JohnnyGOX17/4ch-RF-FE/docs/components/Power/WEBENCH_TPS562208.pdf

## WEBENCH ® Design Report

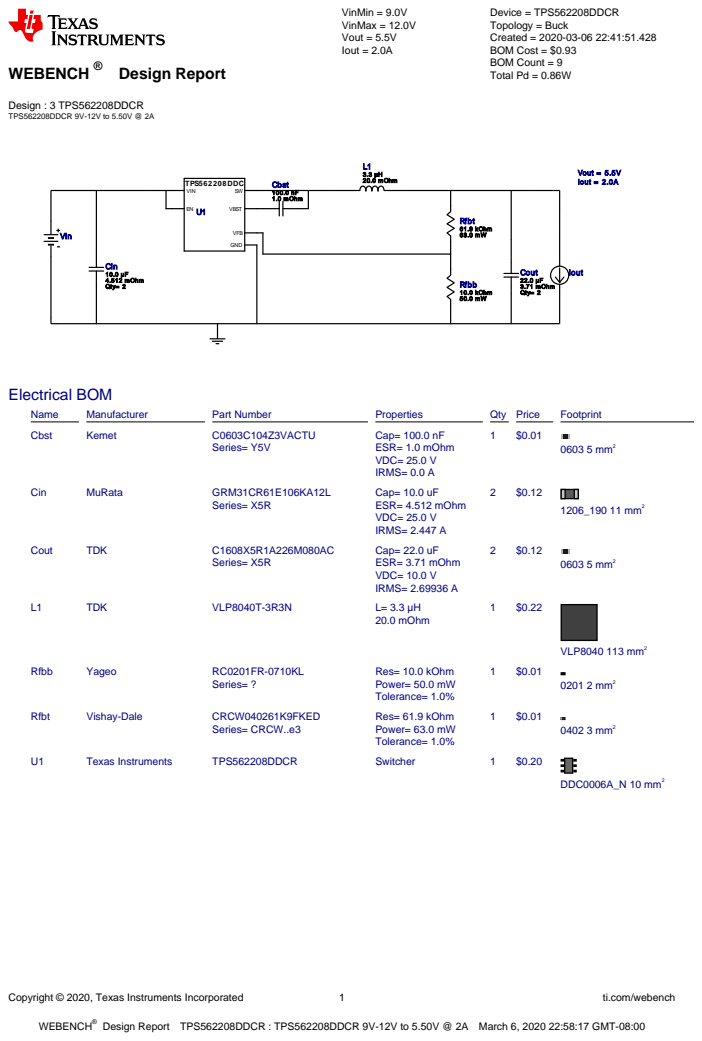
[picture p6: page 1]
Copyright © 2020, Texas Instruments Incorporated; ti.com/webench; WEBENCH®; Design : 3 TPS562208DDCR TPS562208DDCR 9V-12V to 5.50V @ 2A; VinMin = 9.0V VinMax = 12.0V Vout = 5.5V Iout = 2.0A; Device = TPS562208DDCR Topology = Buck Created = 2020-03-06 22:41:51.428 BOM Cost = $0.93 BOM Count = 9 Total Pd = 0.86W; Vout = 5.5V Iout = 2.0A; Rfbb 10.0 kOhm 50.0 mW; Cbst 100.0 nF 1.0 mOhm; Cout 22.0 µF 3.71 mOhm Qty= 2; TPS562208DDC; GND; VIN; VFB; VBST U1; L1 3.3 µH 20.0 mOhm; Rfbt 61.9 kOhm 63.0 mW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

Design Report TPS562208DDCR : TPS562208DDCR 9V-12V to 5.50V @ 2A March 6, 2020 22:58:17 GMT-08:00

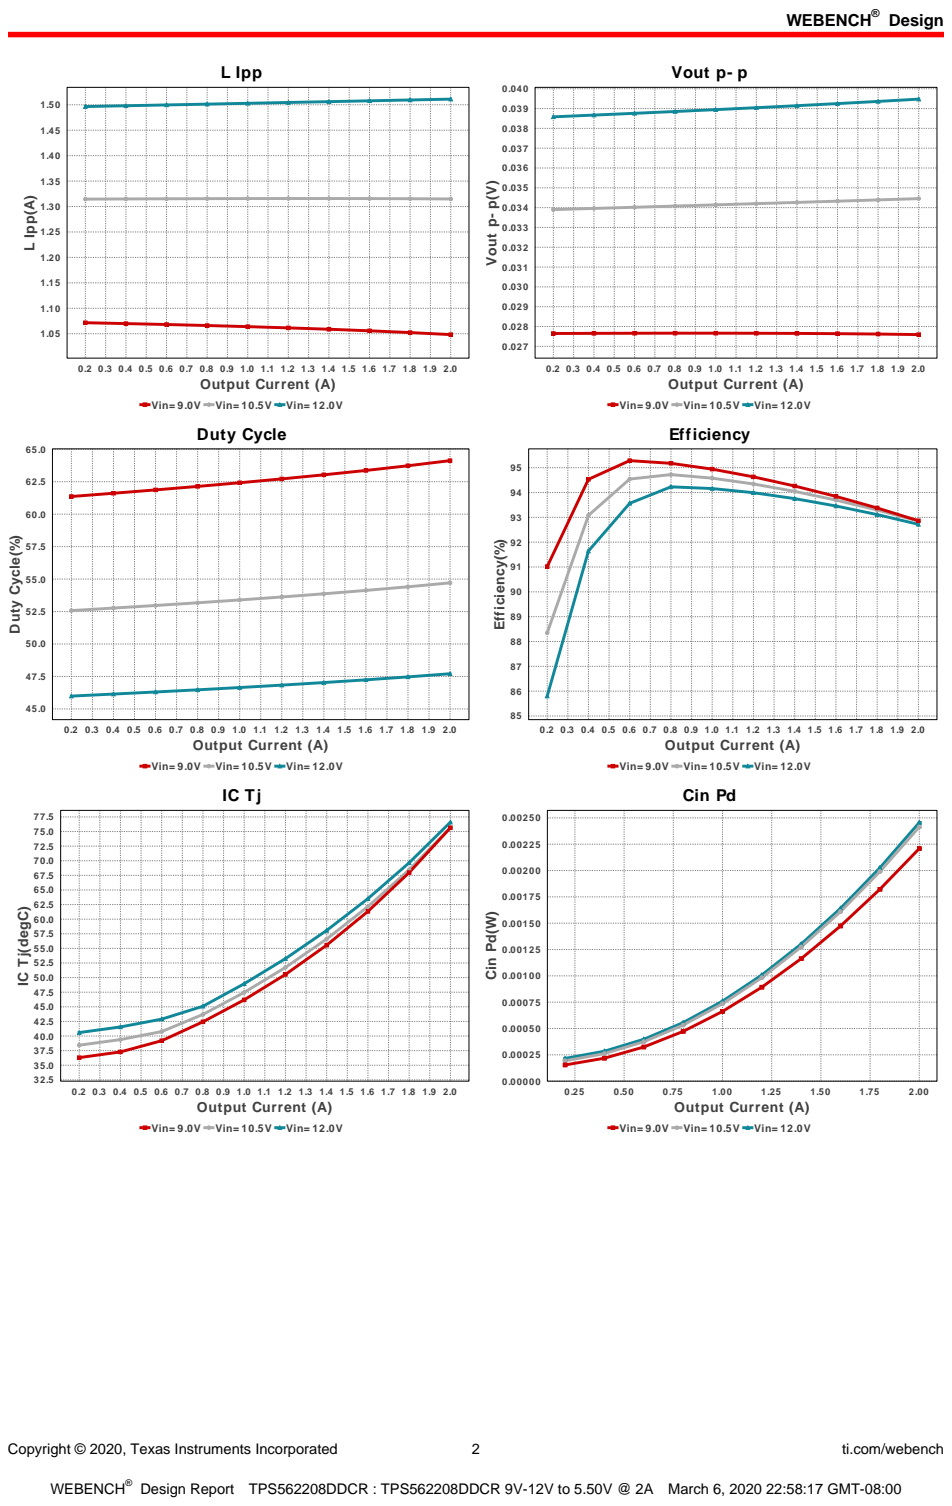
[picture p7: page 2]
Design; Copyright © 2020, Texas Instruments Incorporated; ti.com/webench; L Ipp; 0.2 0.3 0.4 0.5 0.6 0.7 0.8 0.9 1.0 1.1 1.2 1.3 1.4 1.5 1.6 1.7 1.8 1.9 2.0 Output Current (A); L Ipp(A); Vout p- p; Vout p- p(V); Duty Cycle(%); Efficiency(%); Cin Pd; 2.00 Output Current (A); Cin Pd(W)

Vin= 9.0V Vin= 10.5V Vin= 12.0V
Duty Cycle

Efficiency

IC Tj(degC)

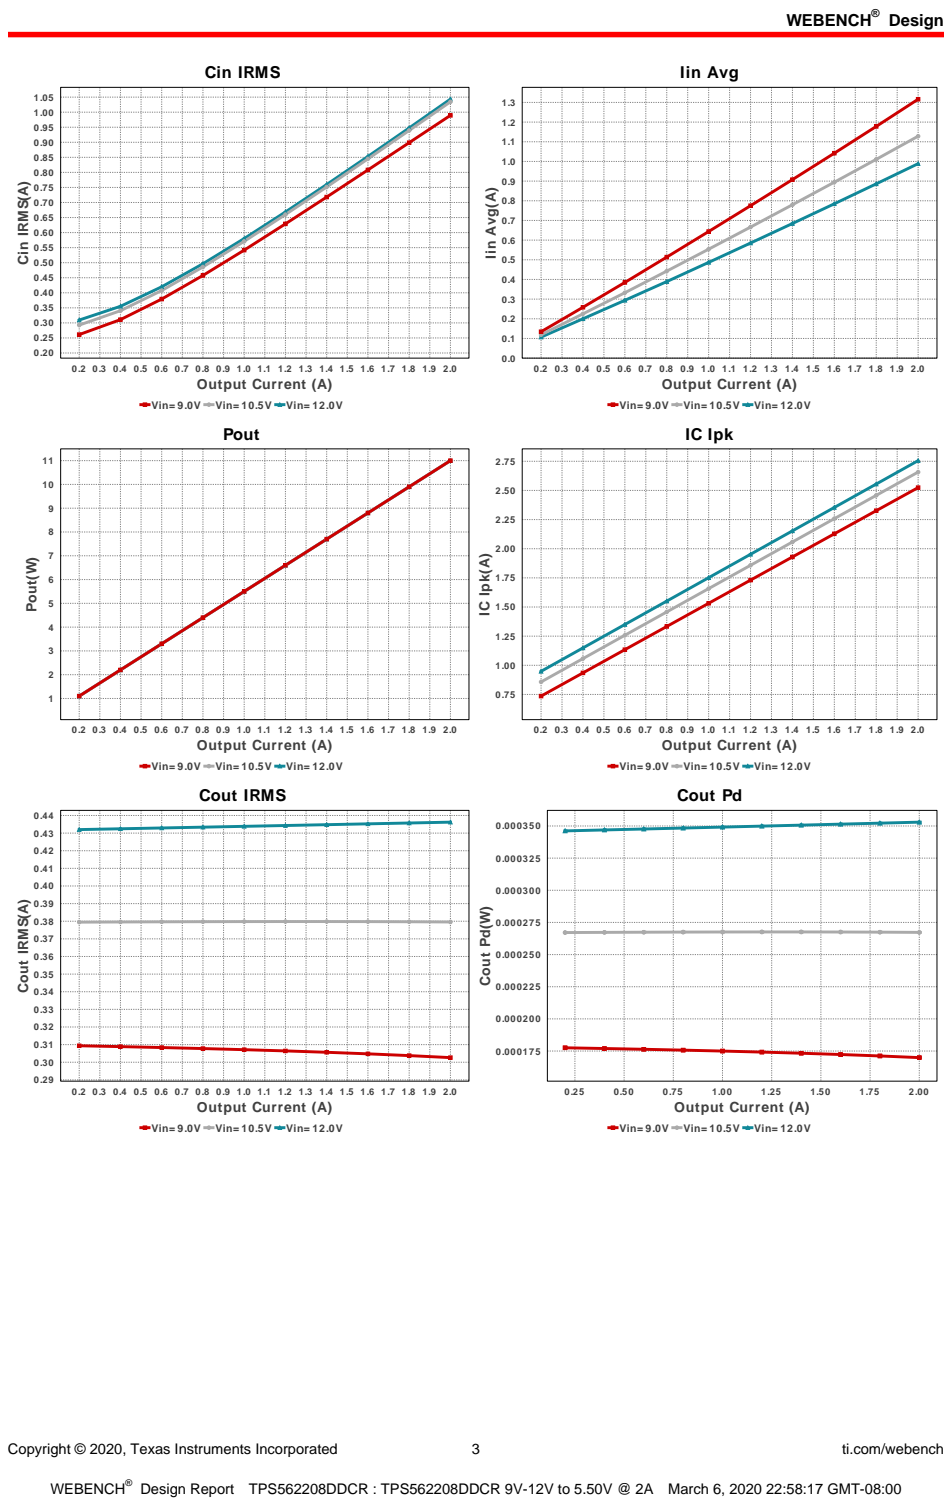
[picture p8: page 3]
Copyright © 2020, Texas Instruments Incorporated; ti.com/webench; Cin IRMS; 0.2 0.3 0.4 0.5 0.6 0.7 0.8 0.9 1.0 1.1 1.2 1.3 1.4 1.5 1.6 1.7 1.8 1.9 2.0 Output Current (A); Cin IRMS(A); Iin Avg; Iin Avg(A); Pout; Pout(W); IC Ipk; IC Ipk(A); Cout IRMS(A); 2.00 Output Current (A); Cout Pd(W)

Vin= 9.0V Vin= 10.5V Vin= 12.0V

Cout IRMS

Cout Pd

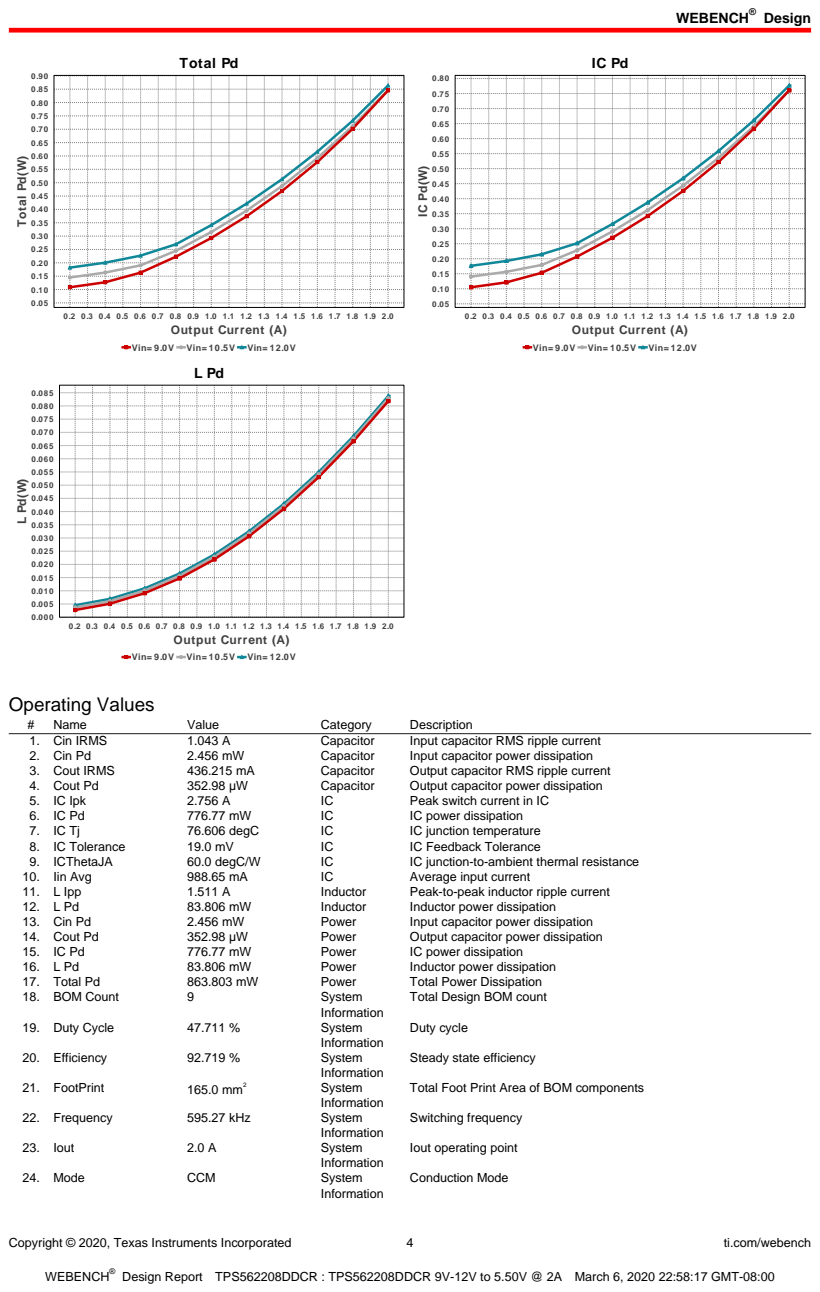
[picture p9: page 4]
Copyright © 2020, Texas Instruments Incorporated; ti.com/webench; Total Pd; 0.2 0.3 0.4 0.5 0.6 0.7 0.8 0.9 1.0 1.1 1.2 1.3 1.4 1.5 1.6 1.7 1.8 1.9 2.0 Output Current (A); Total Pd(W); Operating Values; Name; Value; Category; Description; 1. Cin IRMS; Capacitor; Input capacitor RMS ripple current; 2. Cin Pd; Input capacitor power dissipation; 3. Cout IRMS; Output capacitor RMS ripple current; 4. Cout Pd; Output capacitor power dissipation; 5. IC Ipk; Peak switch current in IC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

Vin= 9.0V Vin= 10.5V Vin= 12.0V

Total Design BOM count

Steady state efficiency

Total Foot Print Area of BOM components

Iout operating point

Copyright © 2020, Texas Instruments Incorporated | 5 | ti.com/webench
# | Name | Value | Category | Description

25. Pout | 11.0 W | System
| | | Information | Total output power
26. Total BOM | $0.93 | System
| | | Information | Total BOM Cost
27. Vin | 12.0 V | System
| | | Information | Vin operating point
28. Vout | 5.5 V | System
| | | Information | Operational Output Voltage
29. Vout Actual | 5.5 V | System
| | | Information | Vout Actual calculated based on selected voltage divider resistors
30. Vout Tolerance | 4.266 % | System
| | | Information | Vout Tolerance based on IC Tolerance (no load) and voltage divider resistors if applicable
31. Vout p-p | 39.476 mV | System
| | | Information | Peak-to-peak output ripple voltage

## Design Inputs

Name | Value | Description
Iout | 2.0 | Maximum Output Current
VinMax | 12.0 | Maximum input voltage
VinMin | 9.0 | Minimum input voltage
Vout | 5.5 | Output Voltage
| base_pn | | TPS562208 | Base Product Number
source | DC | Input Source Type
Ta | 30.0 | Ambient temperature


Copyright © 2020, Texas Instruments Incorporated | 6 | ti.com/webench

## Assembly

## Component Testing

Some published data on components in datasheets such as Capacitor ESR and Inductor DC resistance is based on conservative values that will guarantee that the components always exceed the specification. For design purposes it is usually better to work with typical values. Since this data is not always available it is a good practice to measure the Capacitance and ESR values of Cin and Cout, and the inductance and DC resistance of L1 before assembly of the board. Any large discrepancies in values should be electrically simulated in WEBENCH to check for instabilities and thermally simulated in WebTHERM to make sure critical temperatures are not exceeded.

## Soldering Component to Board

If board assembly is done in house it is best to tack down one terminal of a component on the board then solder the other terminal. For surface mount parts with large tabs, such as the DPAK, the tab on the back of the package should be pre-tinned with solder, then tacked into place by one of the pins. To solder the tab town to the board place the iron down on the board while resting against the tab, heating both surfaces simultaneously. Apply light pressure to the top of the plastic case until the solder flows around the part and the part is flush with the PCB. If the solder is not flowing around the board you may need a higher wattage iron (generally 25W to 30W is enough).

## Initial Startup of Circuit

It is best to initially power up the board by setting the input supply voltage to the lowest operating input voltage 9.0V and set the input supply's current limit to zero. With the input supply off connect up the input supply to Vin and GND. Connect a digital volt meter and a load if needed to set the minimum Iout of the design from Vout and GND. Turn on the input supply and slowly turn up the current limit on the input supply. If the voltage starts to rise on the input supply continue increasing the input supply current limit while watching the output voltage. If the current increases on the input supply, but the voltage remains near zero, then there may be a short or a component misplaced on the board. Power down the board and visually inspect for solder bridges and recheck the diode and capacitor polarities. Once the power supply circuit is operational then more extensive testing may include full load testing, transient load and line tests to compare with simulation results.

## Load Testing

The setup is the same as the initial startup, except that an additional digital voltmeter is connected between Vin and GND, a load is connected between Vout and GND and a current meter is connected in series between Vout and the load. The load must be able to handle at least rated output power + 50% ( 7.5 watts for this design). Ideally the load is supplied in the form of a variable load test unit. It can also be done in the form of suitably large power resistors. When using an oscilloscope to measure waveforms on the prototype board, the ground leads of the oscilloscope probes should be as short as possible and the area of the loop formed by the ground lead should be kept to a minimum. This will help reduce ground lead inductance and eliminate EMI noise that is not actually present in the circuit.

## WEBENCH® Electrical Simulation Report

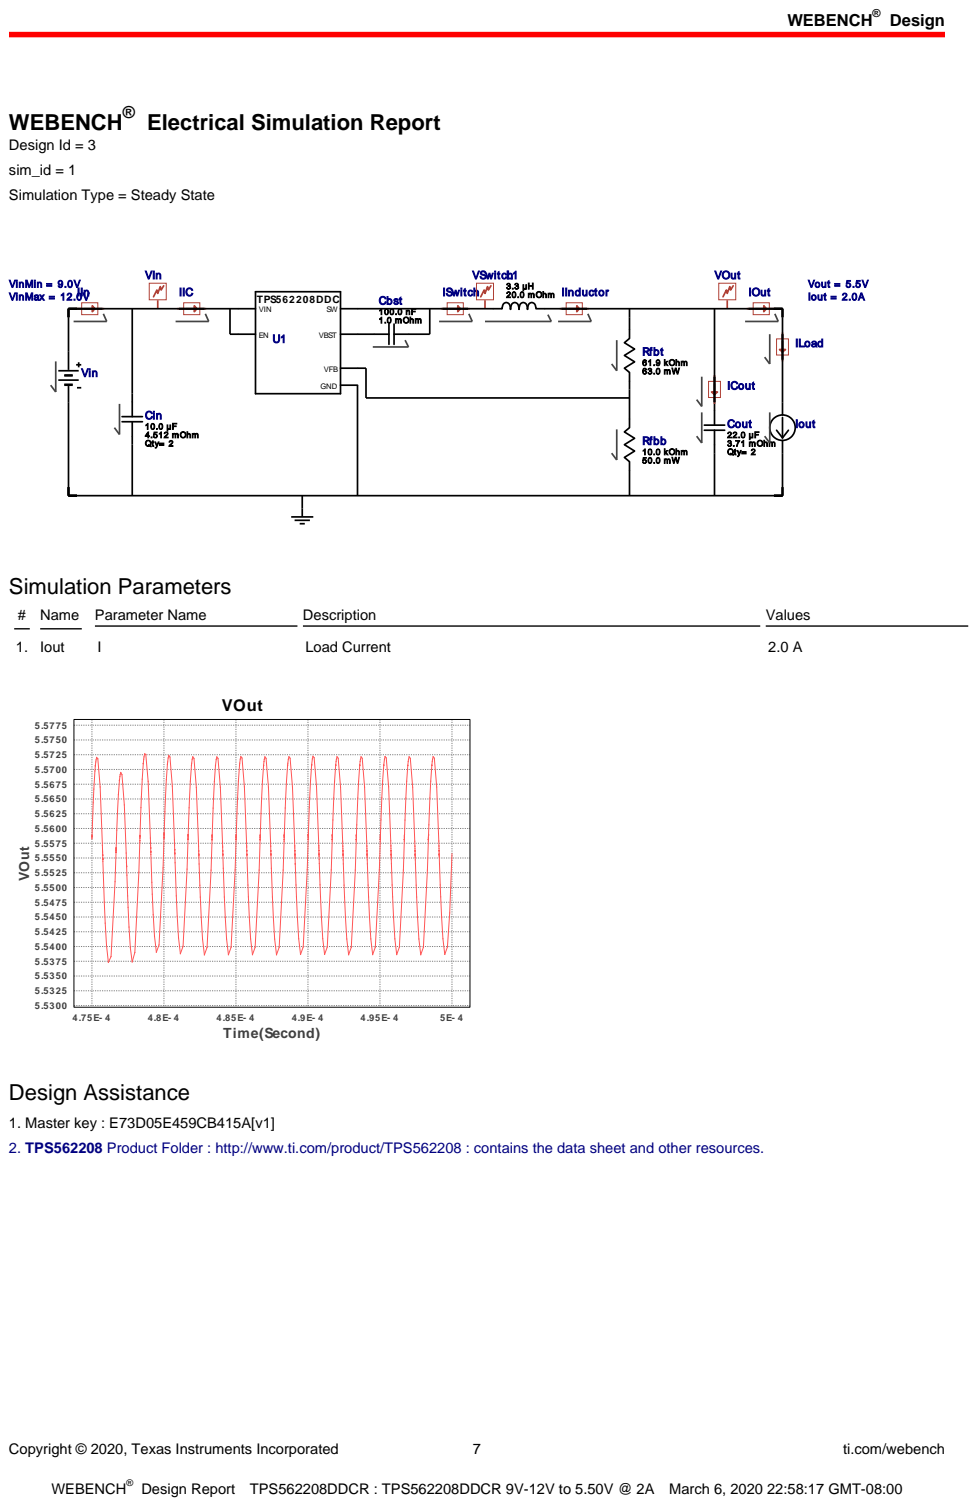
[picture p11: page 7]
Copyright © 2020, Texas Instruments Incorporated; ti.com/webench; IIn; ISwitch; IInductor; IOut; Vout = 5.5V; Iout = 2.0A; VOut; Rfbb 10.0 kOhm 50.0 mW; Cbst 100.0 nF 1.0 mOhm; VSwitch; Cout 22.0 µF 3.71 mOhm Qty= 2; IIC; TPS562208DDC; GND; VIN; VFB; VBST U1; L1 3.3 µH 20.0 mOhm; VinMin = 9.0V VinMax = 12.0V; VIn; ICout; Rfbt 61.9 kOhm 63.0 mW; Cin 10.0 µF 4.512 mOhm Qty= 2; Vin; ILoad; Iout; Simulation Parameters; # Name Parameter Name; Description; Values; 1. Iout; Load Current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

Design Id = 3
sim_id = 1
Simulation Type = Steady State

1. Master key : E73D05E459CB415A[v1]
2. TPS562208 Product Folder : http://www.ti.com/product/TPS562208 : contains the data sheet and other resources.

Copyright © 2020, Texas Instruments Incorporated | 8 | ti.com/webench

Important Notice and Disclaimer

TI provides technical and reliability data (including datasheets), design resources (including reference designs), application or other design advice, web tools, safety information, and other resources AS IS and with all faults, and disclaims all warranties. These resources are intended for skilled developers designing with TI products. You are solely responsible for (1) selecting the appropriate TI products for your application, (2) designing, validating and testing your application, and (3) ensuring your application meets applicable standards, and any other safety, security, or other requirements.

These resources are subject to change without notice. TI grants you permission to use these resources only for development of an application that uses the TI products described in the resource. Other reproduction and display of these resources is prohibited. No license is granted to any other TI intellectual property right or to any third party intellectual property right. TI disclaims responsibility for, and you will fully indemnify TI and its representatives against, any claims, damages, costs, losses, and liabilities arising out of your use of these resources.

Providing these resources does not expand or otherwise alter TI's applicable Terms of Sale or other applicable terms available either on ti.com or provided in conjunction with TI products.
