JohnnyGOX17/4ch-RF-FE/docs/components/Connectors/SMA_TE_1814832.pdf

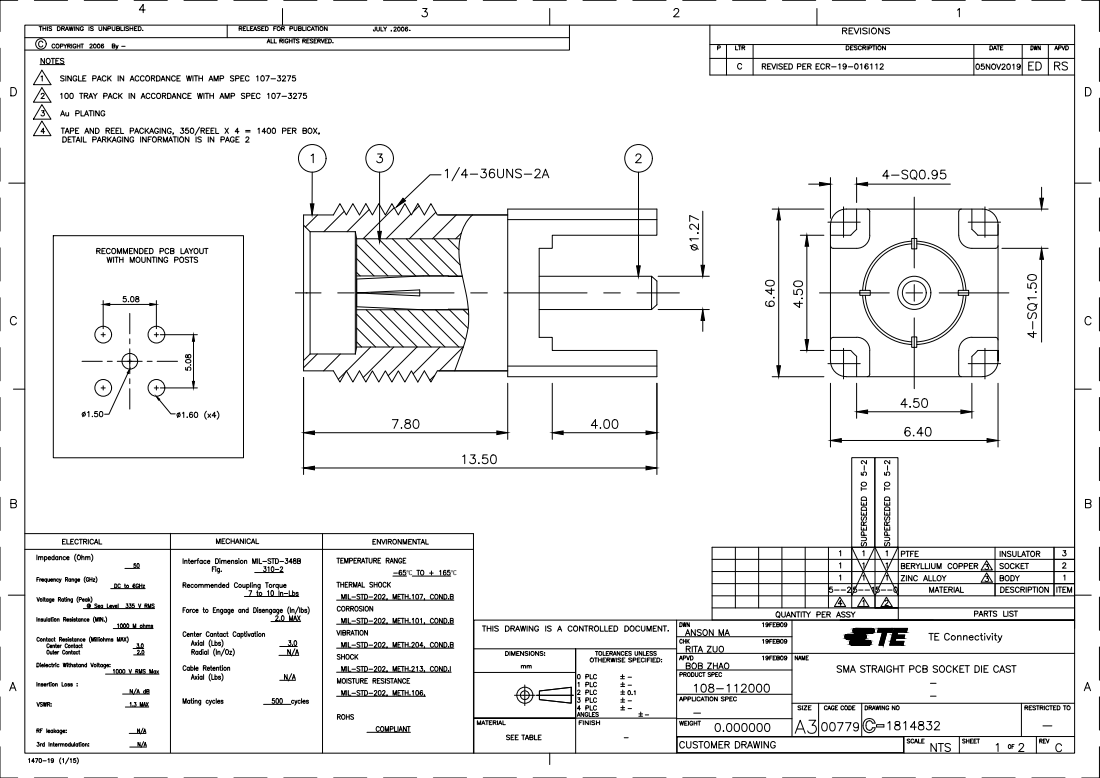
[picture p20: page 1]

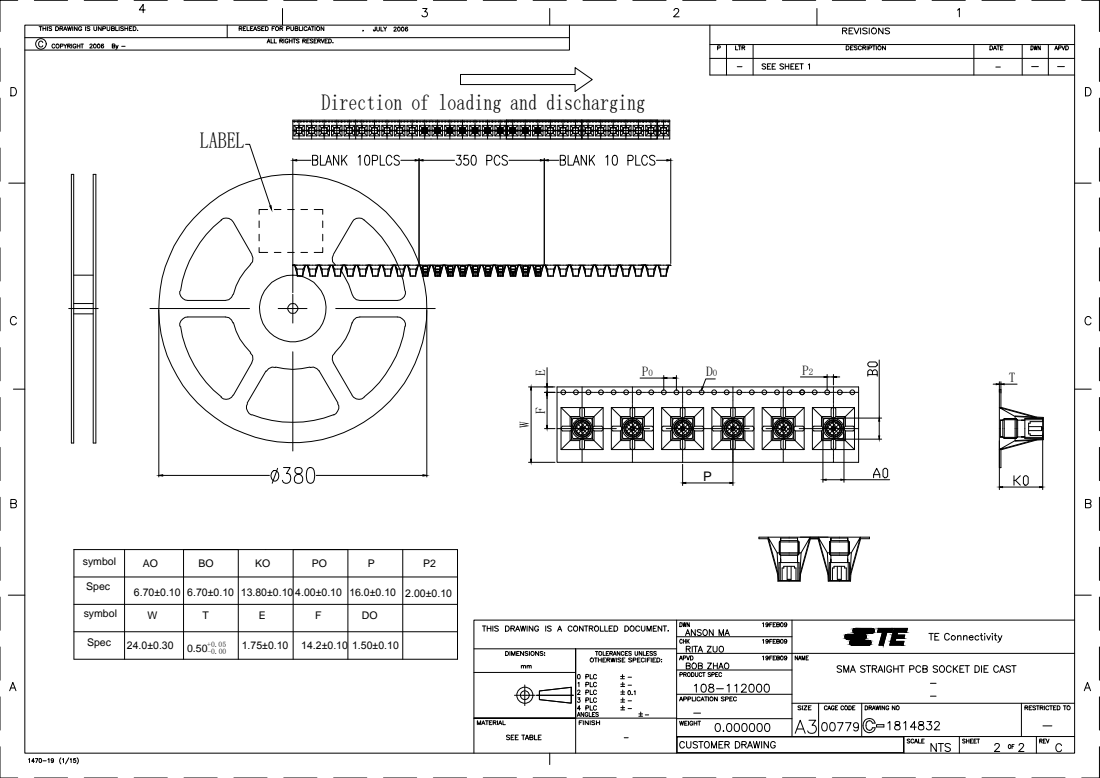
[picture p21: page 2]

Direction of loading and discharging

symbol | AO | BO | KO | PO | P | P2

Spec | 6.70±0.10 | 6.70±0.10 | 13.80±0.10 4.00±0.10 | | 16.0±0.10 | 2.00±0.10

symbol | W | T | E | F | DO

Spec | 24.0±0.30 | 0.50+0.05 -0.00 | 1.75±0.10 | 14.2±0.10 1.50±0.10
